sonocotta/attiny-flasher/firmware/kits/attiny-rainbow-led-light/src/main.h

#define NUMPIXELS 8
#define STATES 3

#define PIN 3
#define NUMPIXELS 8

#define PIN_BTN_1 0
#define PIN_BTN_2 1
#define PIN_BTN_3 2
