sonocotta/attiny-flasher/firmware/kits/attiny-rubber-ducky-mouse/src/main.cpp

#include <DigiMouse.h>
// const int LED_PIN = 1;
const int SHIFT_PX = 5;

void setup() {
  DigiMouse.begin();
  // pinMode(LED_PIN, OUTPUT);
}

// void loop() {
//   digitalWrite(LED_PIN, HIGH);
  
//   DigiMouse.moveY(SHIFT_PX);
//   DigiMouse.moveX(SHIFT_PX);
//   DigiMouse.delay(10);
  
//   DigiMouse.moveY(-2 * SHIFT_PX);
//   DigiMouse.moveX(-2 * SHIFT_PX);
//   DigiMouse.delay(10);

//   DigiMouse.moveY(SHIFT_PX);
//   DigiMouse.moveX(SHIFT_PX);
//   DigiMouse.delay(10);
  
//   digitalWrite(LED_PIN, LOW);
  
//   DigiMouse.delay(30000);
// }


void loop() {
  int8_t x = (millis() % (SHIFT_PX * 2)) - SHIFT_PX;
  DigiMouse.moveX(x);
  int8_t y = (millis() % (SHIFT_PX * 2)) - SHIFT_PX;
  DigiMouse.moveY(y);
  DigiMouse.delay(150);
}
