sonocotta/attiny-flasher/firmware/kits/attiny-led-matrix-rtc-clock-set/src/main.cpp

#include <Arduino.h>
#include <ATtinySerialOut.h>

// CONNECTIONS:
// DS1302 CLK/SCLK --> 5
// DS1302 DAT/IO --> 4
// DS1302 RST/CE --> 2
// DS1302 VCC --> 3.3v - 5v
// DS1302 GND --> GND

#define PIN_SPI_CLK  2
#define PIN_SPI_DATA 0
#define PIN_SPI_CS   1
#define SERIAL_BAUD 115200

#include "ThreeWireInv.h"
#include <RtcDS1302.h>

ThreeWireInv myWire(PIN_SPI_DATA, PIN_SPI_CLK, PIN_SPI_CS); // IO, SCLK, CE
RtcDS1302<ThreeWireInv> Rtc(myWire);

void printDateTime(const RtcDateTime& dt);

void setup () 
{
    Serial.begin(SERIAL_BAUD);

    for (uint8_t a = 0; a <= 9; a++) {
        Serial.print (a);
    }

    Serial.print("compiled: ");
    Serial.print(__DATE__);
    Serial.println(__TIME__);

    Rtc.Begin();

    RtcDateTime compiled = RtcDateTime(__DATE__, __TIME__);
    printDateTime(compiled);
    Serial.println();

    if (!Rtc.IsDateTimeValid()) 
    {
        // Common Causes:
        //    1) first time you ran and the device wasn't running yet
        //    2) the battery on the device is low or even missing

        Serial.println("RTC lost confidence in the DateTime!");
        Rtc.SetDateTime(compiled);
    }

    if (Rtc.GetIsWriteProtected())
    {
        Serial.println("RTC was write protected, enabling writing now");
        Rtc.SetIsWriteProtected(false);
    }

    if (!Rtc.GetIsRunning())
    {
        Serial.println("RTC was not actively running, starting now");
        Rtc.SetIsRunning(true);
    }

    RtcDateTime now = Rtc.GetDateTime();
    if (now < compiled) 
    {
        Serial.println("RTC is older than compile time!  (Updating DateTime)");
        Rtc.SetDateTime(compiled);
    }
    else if (now > compiled) 
    {
        Serial.println("RTC is newer than compile time. (this is expected)");
    }
    else if (now == compiled) 
    {
        Serial.println("RTC is the same as compile time! (not expected but all is fine)");
    }
}

void loop () 
{
    RtcDateTime now = Rtc.GetDateTime();

    printDateTime(now);
    Serial.println();

    if (!now.IsValid())
    {
        // Common Causes:
        //    1) the battery on the device is low or even missing and the power line was disconnected
        Serial.println("RTC lost confidence in the DateTime!");
    }

    delay(3000);
}

#define countof(a) (sizeof(a) / sizeof(a[0]))

void printDateTime(const RtcDateTime& dt)
{
    char datestring[20];

    snprintf_P(datestring, 
            countof(datestring),
            PSTR("%02u/%02u/%04u %02u:%02u:%02u"),
            dt.Month(),
            dt.Day(),
            dt.Year(),
            dt.Hour(),
            dt.Minute(),
            dt.Second() );
    Serial.print(datestring);
}
