sonocotta/attiny-flasher/firmware/flasher/attiny-flasher/src/logo.h

#ifndef _LOGO_H_
#define _LOGO_H_

#ifdef OLED_ENABLE

#define LOGO_BMPWIDTH  64
#define LOGO_BMPHEIGHT 64
#define LOGO_SHOW_MSEC 2000

#ifdef OLED_LIB_ADAFRUIT

    const uint8_t  bitmap_logo[] PROGMEM = {
        0b00000000,0b00000000,0b00000000,0b00000000,0b00000000,0b00000000,0b00000000,0b00000000,
        0b00000000,0b00000000,0b00000000,0b00000000,0b00000000,0b00000000,0b00000000,0b00000000,
        0b00000000,0b00000000,0b00000000,0b00000000,0b00000000,0b00000000,0b00000000,0b00000000,
        0b00000000,0b00000000,0b00000000,0b00000000,0b00000000,0b00000000,0b00000000,0b00000000,
        0b00000000,0b00000000,0b00000000,0b00000000,0b00000000,0b00000000,0b00000000,0b00000000,
        0b00000000,0b00000000,0b00000000,0b11100110,0b01100111,0b00000000,0b00000000,0b00000000,
        0b00000000,0b00000000,0b00000000,0b11100110,0b01100111,0b00000000,0b00000000,0b00000000,
        0b00000000,0b00000000,0b00000000,0b11100110,0b01100111,0b00000000,0b00000000,0b00000000,
        0b00000000,0b00000000,0b00000000,0b11100110,0b01100111,0b00000000,0b00000000,0b00000000,
        0b00000000,0b00000000,0b00000000,0b11100110,0b01100111,0b00000000,0b00000000,0b00000000,
        0b00000000,0b00000000,0b00000000,0b11100110,0b01100111,0b00000000,0b00000000,0b00000000,
        0b00000000,0b00000000,0b00000000,0b11100110,0b01100111,0b00000000,0b00000000,0b00000000,
        0b00000000,0b00000000,0b00000000,0b11100110,0b01100111,0b00000000,0b00000000,0b00000000,
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
    };

#endif
#endif

#endif
