sonocotta/attiny-flasher/firmware/kits/attiny-ir-messenger-send-receive/src/ATtinySerialOut.h

/*
 * ATtinySerialOut.h
 *
 *  Copyright (C) 2015-2020  Armin Joachimsmeyer
 *  Email: armin.joachimsmeyer@gmail.com
 *
 *  This file is part of TinySerialOut https://github.com/ArminJo/ATtinySerialOut.
 *
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
 */

//
// ATMEL ATTINY85
//
//                                               +-\/-+
//               PCINT5/!RESET/ADC0/dW (5) PB5  1|    |8  VCC
// USB+   PCINT3/XTAL1/CLKI/!OC1B/ADC3 (3) PB3  2|    |7  PB2 (2) SCK/USCK/SCL/ADC1/T0/INT0/PCINT2 / TX Debug output
// USB-   PCINT4/XTAL2/CLKO/ OC1B/ADC2 (4) PB4  3|    |6  PB1 (1) MISO/DO/AIN1/OC0B/ OC1A/PCINT1 - (Digispark) LED
//                                         GND  4|    |5  PB0 (0) MOSI/DI/AIN0/OC0A/!OC1A/SDA/AREF/PCINT0
//                                               +----+

// ATMEL ATTINY167
// Pin numbers are for Digispark core
// Pin numbers in Parenthesis are for ATTinyCore
//
//                    +-\/-+
//    RX  6 (0) PA0  1|    |20  PB0 (D8)  0 OC1AU  TONE  Timer 1 Channel A
//    TX  7 (1) PA1  2|    |19  PB1 (9)  1 OC1BU  Internal LED
//        8 (2) PA2  3|    |18  PB2 (10) 2 OC1AV  Timer 1 Channel B
//   INT1 9 (3) PA3  4|    |17  PB3 (11) 4 OC1BV  connected with 51 Ohm to D- and 3.3 volt Zener.
//             AVCC  5|    |16  GND
//             AGND  6|    |15  VCC
//       10 (4) PA4  7|    |14  PB4 (12) XTAL1
//       11 (5) PA5  8|    |13  PB5 (13) XTAL2
//       12 (6) PA6  9|    |12  PB6 (14) 3 INT0  connected with 68 Ohm to D+ (and disconnected 3.3 volt Zener). Is terminated with ~20 kOhm if USB attached :-(
//        5 (7) PA7 10|    |11  PB7 (15) RESET
//                    +----+
//

#ifndef ATTINY_SERIAL_OUT_H_
#define ATTINY_SERIAL_OUT_H_

#if defined(__AVR_ATtiny25__) || defined(__AVR_ATtiny45__) || defined(__AVR_ATtiny85__) \
    || defined(__AVR_ATtiny24__) || defined(__AVR_ATtiny44__) || defined(__AVR_ATtiny84__) \
    || defined(__AVR_ATtiny87__) || defined(__AVR_ATtiny167__)
#include <Arduino.h>

#define VERSION_ATTINY_SERIAL_OUT "1.2.1"
#define VERSION_ATTINY_SERIAL_OUT_MAJOR 1
#define VERSION_ATTINY_SERIAL_OUT_MINOR 2

#if (F_CPU != 1000000) &&  (F_CPU != 8000000) &&  (F_CPU != 16000000)
#error F_CPU value must be 1000000, 8000000 or 16000000.
#endif

#if defined(__AVR_ATtiny87__) || defined(__AVR_ATtiny167__)
#  ifndef TX_PIN
#define TX_PIN PA1 // (package pin 2 / TXD on Tiny167) - can use one of PA0 to PA7 here
#  endif
#else // defined(__AVR_ATtiny87__) || defined(__AVR_ATtiny167__)
#  ifndef TX_PIN
#define TX_PIN PB4 // (package pin 7 on Tiny85) - can use one of PB0 to PB4 (+PB5) here
#  endif
#endif

/*
 * Activate this, if you want to save 10 bytes code size and if you can live
 * with 87 micro seconds intervals of disabled interrupts for each sent byte @115200 baud.
 */
//#define USE_ALWAYS_CLI_SEI_GUARD_FOR_OUTPUT

/*
 * @1 MHz use bigger (+120 bytes for unrolled loop) but faster code. Otherwise only 38400 baud is possible.
 * @8/16 MHz use 115200 baud instead of 230400 baud.
 */
//#define TINY_SERIAL_DO_NOT_USE_115200BAUD
#ifndef TINY_SERIAL_DO_NOT_USE_115200BAUD  // define this to force using other baud rates
#define USE_115200BAUD
#endif

// The same class definition as for plain arduino
#if not defined(F)
class __FlashStringHelper;
#define F(string_literal) (reinterpret_cast<const __FlashStringHelper *>(PSTR(string_literal)))
#endif

extern bool sUseCliSeiForWrite; // default is true
void useCliSeiForStrings(bool aUseCliSeiForWrite); // might be useful to set to false if output is done from ISR, to avoid to call unwanted sei().

void initTXPin();
void write1Start8Data1StopNoParity(uint8_t aValue);
void write1Start8Data1StopNoParityWithCliSei(uint8_t aValue);
void writeValue(uint8_t aValue);

void writeString(const char *aStringPtr);
void writeString(const __FlashStringHelper *aStringPtr);
void writeString_P(const char *aStringPtr);
void writeString_E(const char *aStringPtr);
void writeStringWithCliSei(const char *aStringPtr);
void writeStringWithoutCliSei(const char *aStringPtr);
void writeStringSkipLeadingSpaces(const char *aStringPtr);

void writeBinary(uint8_t aByte); // write direct without decoding
void writeChar(uint8_t aChar); // Synonym for writeBinary
void writeCRLF();
void writeByte(int8_t aByte);
void writeUnsignedByte(uint8_t aByte);
void writeUnsignedByteHex(uint8_t aByte);
void writeUnsignedByteHexWithPrefix(uint8_t aByte);
void writeInt(int16_t aInteger);
void writeUnsignedInt(uint16_t aInteger);
void writeLong(int32_t aLong);
void writeUnsignedLong(uint32_t aLong);
void writeFloat(double aFloat);
void writeFloat(double aFloat, uint8_t aDigits);

char nibbleToHex(uint8_t aByte);

class TinySerialOut
{
public:

    void begin(long);
    void end();
    void flush(void);

    void printHex(uint8_t aByte); // with 0x prefix
    void printHex(uint16_t aWord); // with 0x prefix
    void printlnHex(uint8_t aByte); // with 0x prefix
    void printlnHex(uint16_t aWord); // with 0x prefix

    // virtual functions of Print class
    size_t write(uint8_t aByte);
    operator bool(); // To support "while (!Serial); // wait for serial port to connect. Required for Leonardo only

    void print(const __FlashStringHelper *aStringPtr);
    void print(const char *aStringPtr);
    void print(char aChar);
    void print(uint8_t aByte, uint8_t aBase = 10);
    void print(int16_t aInteger, uint8_t aBase = 10);
    void print(uint16_t aInteger, uint8_t aBase = 10);
    void print(int32_t aLong, uint8_t aBase = 10);
    void print(uint32_t aLong, uint8_t aBase = 10);
    void print(double aFloat, uint8_t aDigits = 2);

    void println(const char *aStringPtr);
    void println(const __FlashStringHelper *aStringPtr);
    void println(char aChar);
    void println(uint8_t aByte, uint8_t aBase = 10);
    void println(int16_t aInteger, uint8_t aBase = 10);
    void println(uint16_t aInteger, uint8_t aBase = 10);
    void println(int32_t aLong, uint8_t aBase = 10);
    void println(uint32_t aLong, uint8_t aBase = 10);
    void println(double aFloat, uint8_t aDigits = 2);

    void println(void);

};

// #if ... to be compatible with ATTinyCores and AttinyDigisparkCores
#if (!defined(UBRRH) && !defined(UBRR0H)) /*AttinyDigisparkCore and AttinyDigisparkCore condition*/ \
    || USE_SOFTWARE_SERIAL /*AttinyDigisparkCore condition*/\
    || ((defined(UBRRH) || defined(UBRR0H) || defined(UBRR1H) || defined(LINBRRH)) && !USE_SOFTWARE_SERIAL)/*AttinyDigisparkCore condition for HardwareSerial*/
// Switch to SerialOut since Serial is already defined
// or activate line 745 in TinyDebugSerial.h included in AttinyDigisparkCores/src/tiny/WProgram.h at line 24 for AttinyDigisparkCores
extern TinySerialOut SerialOut;
#define Serial SerialOut
#else
#  if defined(Serial)
#undef Serial
#  endif
extern TinySerialOut Serial;
#endif
#define Print TinySerialOut

#endif // defined(__AVR_ATtiny25__) || defined(__AVR_ATtiny45__) || defined(__AVR_ATtiny85__) || defined(__AVR_ATtiny87__) || defined(__AVR_ATtiny167__)

#endif /* ATTINY_SERIAL_OUT_H_ */

#pragma once
